blazjerman/DDC-Manual/images/rectified_ripple.png

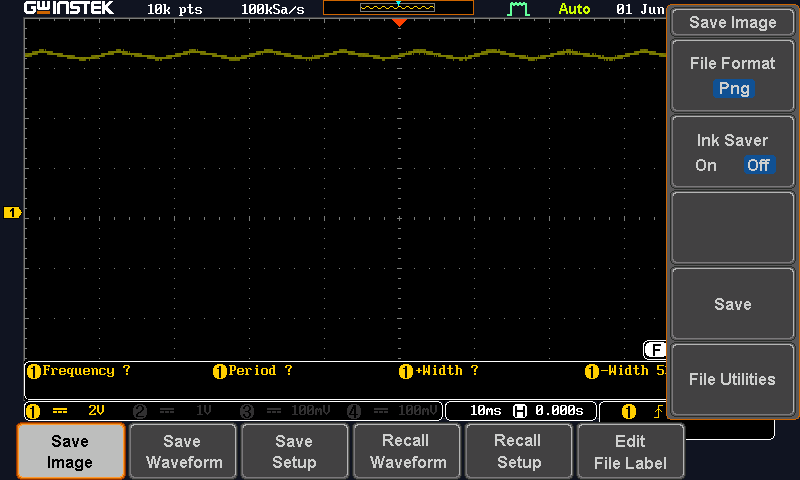
images/rectified_ripple.png
